poggersv2/keybard/assets/cad/DSA Keycap Set, 8mm - 2172302/images/2ad13d2d48048c0d299474afba5edf35.png

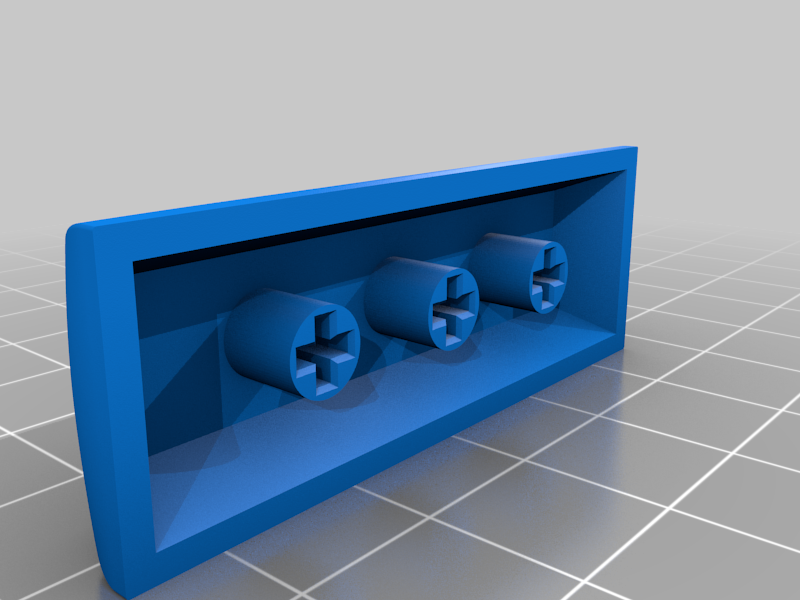
assets/cad/DSA Keycap Set, 8mm - 2172302/images/2ad13d2d48048c0d299474afba5edf35.png
