poggersv2/keybard/assets/cad/DSA Keycap Set, 8mm - 2172302/images/5f5187d77f289929aafdf7cb9bf8af5c.png

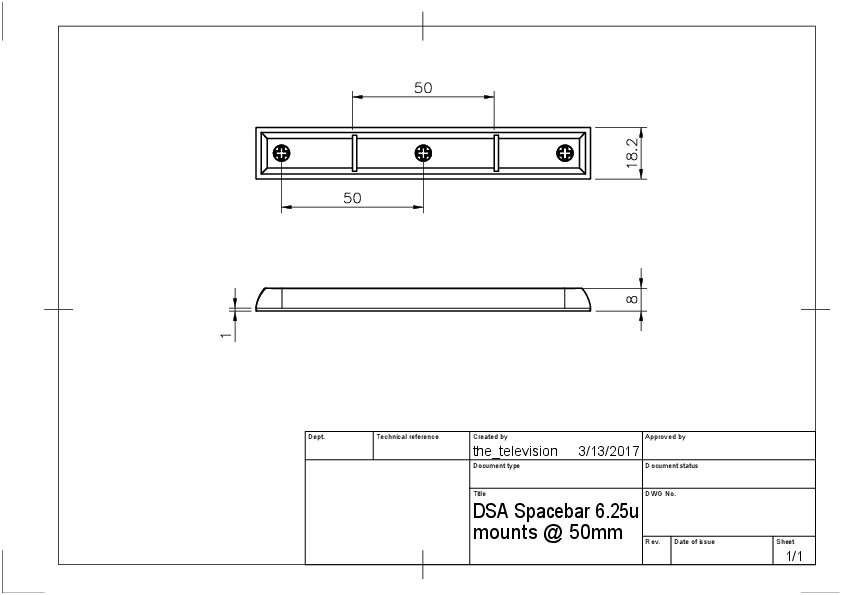
assets/cad/DSA Keycap Set, 8mm - 2172302/images/5f5187d77f289929aafdf7cb9bf8af5c.png
