poggersv2/keybard/assets/cad/DSA Keycap Set, 8mm - 2172302/images/7d493ce8c5c8efaf1bbd04a6a6fb81b1.png

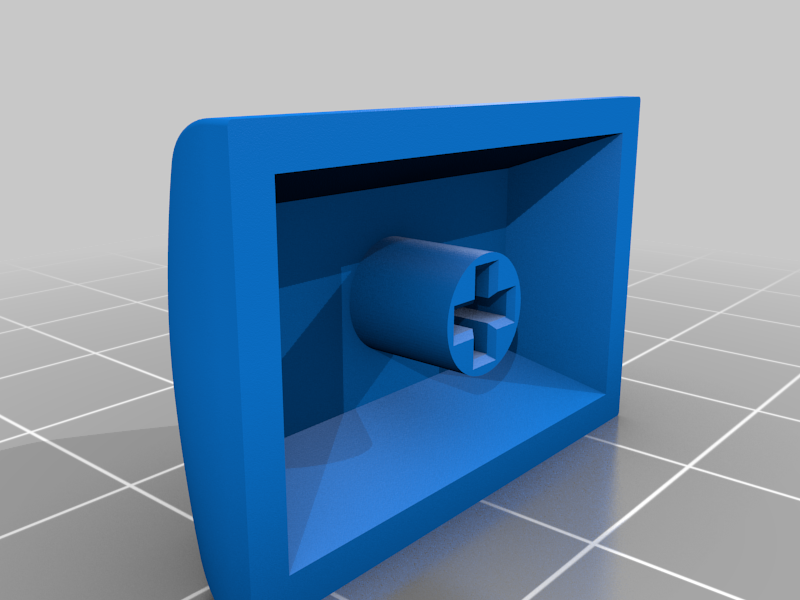
assets/cad/DSA Keycap Set, 8mm - 2172302/images/7d493ce8c5c8efaf1bbd04a6a6fb81b1.png
