poggersv2/keybard/assets/cad/DSA Keycap Set, 8mm - 2172302/images/356e64272c345fa081fa692bff33496e.png

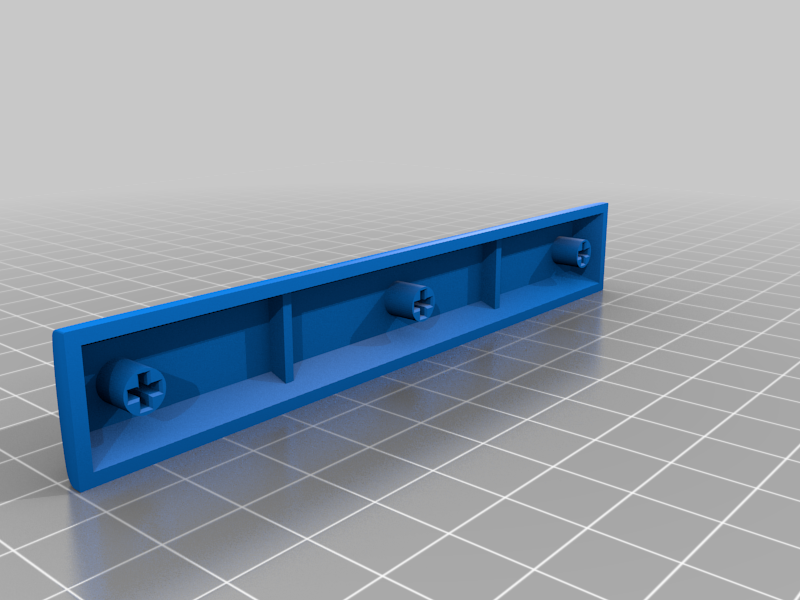
assets/cad/DSA Keycap Set, 8mm - 2172302/images/356e64272c345fa081fa692bff33496e.png
