poggersv2/keybard/assets/cad/DSA Keycap Set, 8mm - 2172302/images/77507969cdad141a6ee3feddd2aee868.png

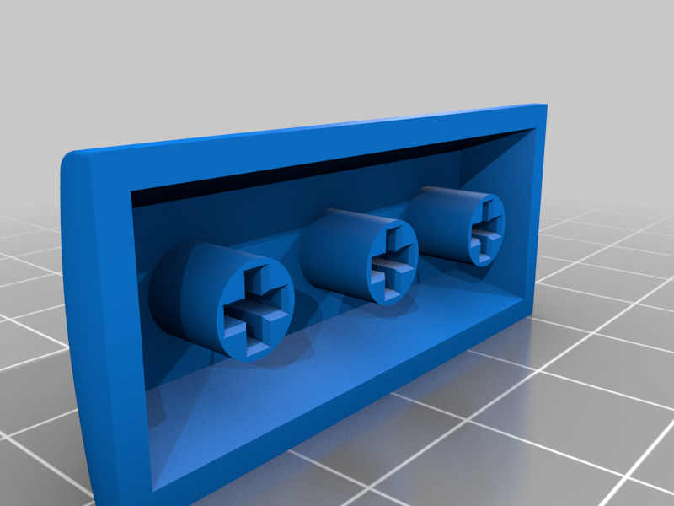
assets/cad/DSA Keycap Set, 8mm - 2172302/images/77507969cdad141a6ee3feddd2aee868.png
