poggersv2/keybard/assets/cad/DSA Keycap Set, 8mm - 2172302/images/dff3dd0c02cce0c457e0ab397aca72e7.png

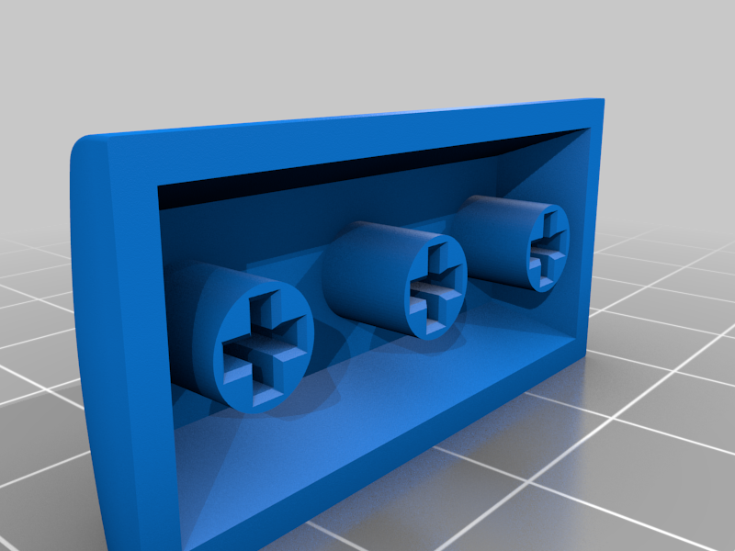
assets/cad/DSA Keycap Set, 8mm - 2172302/images/dff3dd0c02cce0c457e0ab397aca72e7.png
