poggersv2/keybard/assets/cad/DSA Keycap Set, 8mm - 2172302/images/e9ec1d3fcec00315cf30b883f8e49805.png

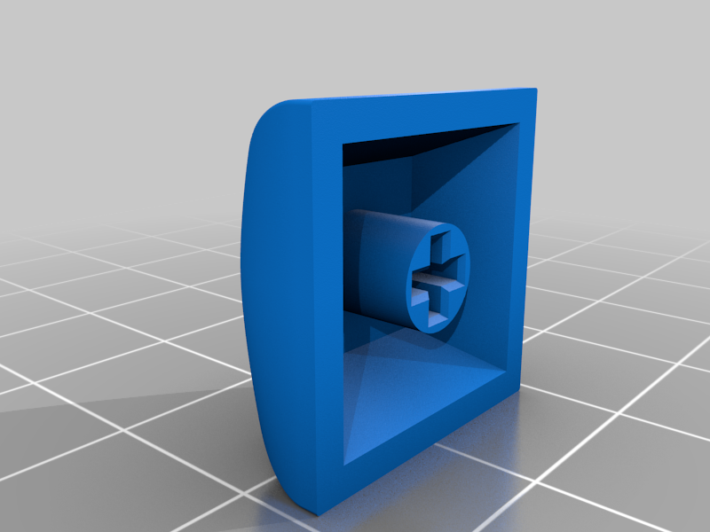
assets/cad/DSA Keycap Set, 8mm - 2172302/images/e9ec1d3fcec00315cf30b883f8e49805.png
