poggersv2/keybard/assets/cad/DSA Keycap Set, 8mm - 2172302/files/DSA_Spacebar_6.25u_50mm_spacing.step

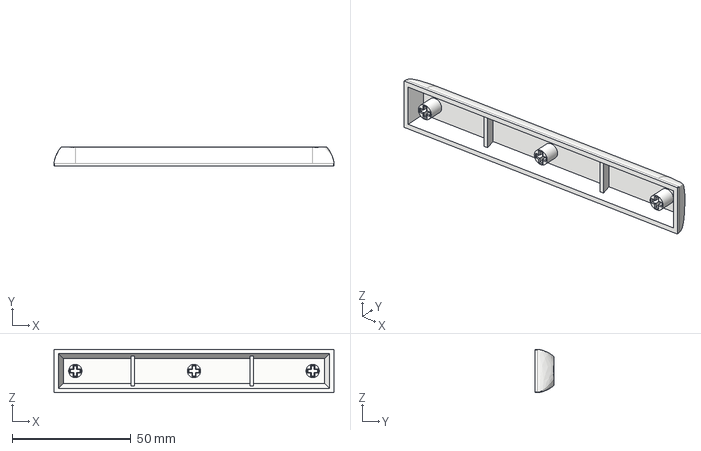
[picture p26: CAD file, 2026-07-20]
assets/cad/DSA Keycap Set, 8mm - 2172302/files/DSA_Spacebar_6.25u_50mm_spacing.step
118.0 x 8.00 x 18.2 mm
