poggersv2/keybard/assets/cad/DSA Keycap Set, 8mm - 2172302/files/DSA_2.75u.step

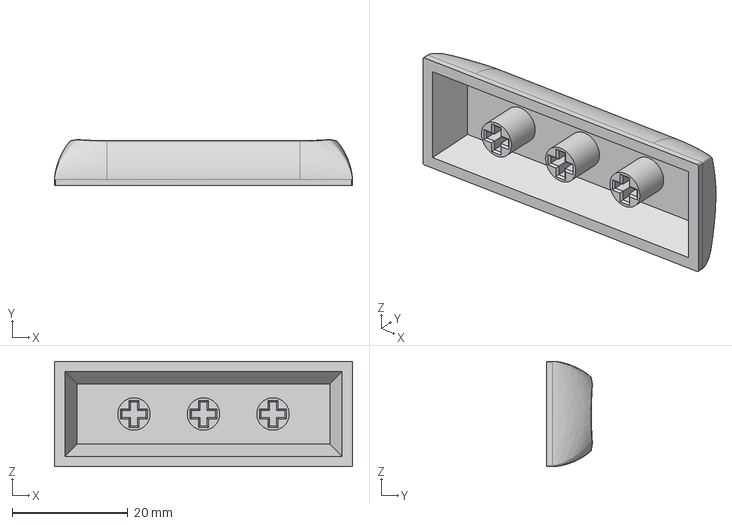
[picture p29: CAD file, 2026-07-20]
assets/cad/DSA Keycap Set, 8mm - 2172302/files/DSA_2.75u.step
51.5 x 7.91 x 18.2 mm
